DaveBerkeley/audio_selector/gateware/build.py

#!/usr/bin/env python

from amaranth import *
from amaranth.build import *

from audio_selector import System, get_resources

#
#

def ext_clock(freq, Platform, ck_name="ckext"):
    # Override the on-board clock with an external one
    class _Platform(Platform):
        default_clk = ck_name
        ck_freq = freq

    return _Platform()

#
#

if __name__ == "__main__":

    import argparse

    parser = argparse.ArgumentParser()
    parser.add_argument("--dot", help="generate Stream graph")
    parser.add_argument("--prog", action="store_true")
    parser.add_argument("--verbose", action="store_true")
    parser.add_argument("--freq", type=float, default=27e6*2)
    parser.add_argument("--platform", default="tangnano")
    parser.add_argument("--system")

    args = parser.parse_args()

    if args.platform == "tangnano":
        from tang_nano_dock import TangNanoDock as Platform
    elif args.platform == "i9":
        from colorlight_i9_r7_2 import Colorlight_i9_R72Platform as Platform
    elif args.platform == "icebreaker":
        from amaranth_boards.icebreaker import ICEBreakerPlatform as Platform
    elif args.platform == "icesugarnano":
        from amaranth_boards.icesugar_nano import ICESugarNanoPlatform as Platform

    freq = args.freq
    # external clock
    ext_freq = 48e3 * 512 # External MCK from I2S pin
    ext_freq = 48e3 * 1024 # External Xtal on PMOD
    freq = ext_freq

    platform = ext_clock(freq, Platform)

    r = get_resources(platform, args.platform, args.system, lang="Amaranth")
    platform.add_resources(r)

    # TODO : select other systems?
    dut = System(freq)
    # TODO : how are the clock constraints passed to Amaranth?
    #platform.add_clock_constraint(s, freq)

    platform.build(dut, do_program=args.prog, verbose=args.verbose)

    # Generate DOT graph of the Amaranth Streams
    if args.dot:
        from streams import dot
        dot_path = "/tmp/wifi.dot"
        png_path = args.dot
        dot.graph(dut, dot_path, png_path)

#   FIN
