DaveBerkeley/audio_selector/gateware/audio_selector.py

from amaranth import *
from amaranth.utils import bits_for

from streams import Stream, Join, Sink, Arbiter, Tee, Split
from streams.spi import SpiPeripheral
from streams.i2s import I2SRxClock, I2STxClock, I2SInputLR, I2SOutput
from streams.route import Router, Select
from streams.spdif import SPDIF_Tx, SPDIF_Rx
from streams.monitor import Monitor
from streams.ws2812 import LedStream
from streams.ops import Enumerate

#import pll

from gpio import GpioOut, GpioIn

from ppm import StereoAbs, PPM, BarGraph

audio = 16
audio_layout = [("data", audio)]
control = 32
control_layout = [("data", control)]
left_layout = [("left", audio)]
right_layout = [("right", audio)]
stereo_layout = left_layout + right_layout
led_layout = [("addr", 8), ("r", 8), ("g", 8), ("b", 8), ]

#
#

class TR:
    # Top-level Router 
    GPIO = 0
    LED = 1
    SELECT = 2
    MONITOR = 6
    KEYS = 16

routes = [
    #TR.GPIO,
    TR.LED,
    #TR.MONITOR,
    #TR.SELECT,
    TR.KEYS,
]

#
#

class UI(Elaboratable):

    KEY_SW = 0x01
    KEY_A  = 0x04
    KEY_B  = 0x02

    def __init__(self, chans=5):
        keys = 3
        leds = 8
        bright = 0xff
        self.nkeys = keys
        self.chans = chans
        self.bright = bright

        self.keys = Stream(layout=[("data", keys)], name="keys")
        self.i = Stream(layout=led_layout, name="i")
        self.o = Stream(layout=led_layout, name="o")

        self.key_state = Signal(keys)

        self.channel = Signal(range(chans))
        self.edit = Signal(range(chans))
        self.edit_mode = Signal()

        self.leds = leds
        self.led = Signal(range(leds+1))
        self.update = Signal()

    def elaborate(self, _):
        m = Module()

        with m.If(self.o.valid & self.o.ready):
            m.d.sync += self.o.valid.eq(0)
        with m.If(~self.i.ready):
            m.d.sync += self.i.ready.eq(1)
        with m.If(self.i.valid & self.i.ready):
            m.d.sync += self.i.ready.eq(0)
            # copy in to out, unless in edit_mode
            with m.If(~self.edit_mode):
                m.d.sync += self.o.valid.eq(1)
                m.d.sync += self.o.payload_eq(self.i.cat_payload(flags=True), flags=True)

        # Update LED output with the edit_mode state
        with m.If(self.update | self.led):
            with m.If(~self.o.valid):
                m.d.sync += [
                    self.o.valid.eq(1),
                    self.o.first.eq(self.led==0),
                    self.o.last.eq(self.led==(self.leds-1)),
                    self.o.addr.eq(self.led),
                    self.o.r.eq(0),
                    self.o.g.eq(0),
                    self.o.b.eq(0),

                    self.led.eq(self.led + 1),
                    self.update.eq(0),
                ]
                with m.If(self.led == self.channel):
                    m.d.sync += self.o.r.eq(self.bright)
                with m.If(self.led == self.edit):
                    m.d.sync += self.o.g.eq(self.bright)

                with m.If(self.led == (self.leds-1)):
                    m.d.sync += self.led.eq(0)

        with m.If((~self.keys.ready) & (self.led == 0)):
            m.d.sync += self.keys.ready.eq(1)

        key_on = Signal(self.nkeys)
        key_off = Signal(self.nkeys)
        key_diff = Signal(self.nkeys)
        m.d.comb += [
            key_on.eq(self.keys.data & ~self.key_state),
            key_off.eq(self.key_state & ~self.keys.data),
            key_diff.eq(self.key_state ^ self.keys.data),
        ]

        with m.If(self.keys.valid & self.keys.ready):
            m.d.sync += self.keys.ready.eq(0)
            m.d.sync += self.key_state.eq(self.keys.data)
            # process key input
            with m.If(self.edit_mode):
                # in edit mode
                with m.If(key_on & self.KEY_SW):
                    # enter the selection, exit edit_mode
                    m.d.sync += [
                        self.channel.eq(self.edit),
                        self.edit_mode.eq(0),
                    ]
                with m.If(key_on & self.KEY_A):
                    # change the channel
                    m.d.sync += [
                        self.update.eq(1),
                    ]
                    with m.If(self.keys.data & self.KEY_B):
                        # increment edit channel
                        with m.If(self.edit == (self.chans-1)):
                            m.d.sync += self.edit.eq(0)
                        with m.Else():
                            m.d.sync += self.edit.eq(self.edit + 1)
                    with m.Else():
                        # decrement edit channel
                        with m.If(self.edit == 0):
                            m.d.sync += self.edit.eq(self.chans - 1)
                        with m.Else():
                            m.d.sync += self.edit.eq(self.edit - 1)

            with m.Else():
                # currently in pass-thru mode
                with m.If(key_on & self.KEY_SW):
                    # switch to edit_mode
                    m.d.sync += [
                        self.edit_mode.eq(1),
                        self.edit.eq(self.channel),
                        self.update.eq(1),
                    ]

        return m

#
#

class Meter(Elaboratable):

    def __init__(self, thresholds=[]):
        self.mods = []
        self.connects = []

        led_width = 8
        bar_len = len(thresholds)
        bar_layout = [("data", led_width)]
        self.i = Stream(layout=stereo_layout, name="i")

        self.abs = StereoAbs(layout=stereo_layout)
        self.mods += [ self.abs ]
        self.connects += [ (self.i, self.abs.i) ]

        self.ppm = PPM(layout=audio_layout)
        self.mods += [ self.ppm ]
        self.connects += [ (self.abs.o, self.ppm.i) ]

        self.bars = BarGraph(iwidth=audio, owidth=led_width, thresholds=thresholds)
        self.mods += [ self.bars ]
        self.connects += [ (self.ppm.o, self.bars.i) ]

        self.enum = Enumerate(idx=[("addr", bits_for(bar_len-1))], layout=bar_layout, offset=0)
        self.mods += [ self.enum ]
        self.connects += [ (self.bars.o, self.enum.i) ]
 
        layout = self.enum.o.get_layout()
        self.o = Stream(layout=layout, name="o")
        self.connects += [ (self.enum.o, self.o) ]

    def elaborate(self, platform):
        m = Module()
        m.submodules += self.mods

        for a, b in self.connects:
            m.d.comb += Stream.connect(a, b)

        return m

#
#

class AudioSelector(Elaboratable):

    def __init__(self, freq):
        self.sys_ck = freq
        self.mods = []
        self.connects = []
        self.comb = []

        has_ci = True # add to TR items?

        if has_ci:
            self.in_arb = Arbiter(layout=control_layout, n=2)
            self.mods += [ self.in_arb ]

            self.ci = Stream(layout=control_layout, name="ci")
            self.connects += [ (self.ci, self.in_arb.i[0]) ]

        self.spi = SpiPeripheral(width=control, last_cs=True)
        self.mods += [ self.spi ]
        if has_ci:
            self.connects += [ (self.spi.o, self.in_arb.i[1]) ]

        sink = True
        self.router = Router(layout=control_layout, addr_field="data", addrs=routes, sink=sink)
        self.mods += [ self.router ]
        if has_ci:
            self.connects += [ (self.in_arb.o, self.router.i) ]
        else:
            self.connects += [ (self.spi.o, self.router.i) ]

        if TR.GPIO in routes:
            self.gpio_led = GpioOut(8, name="gpio.led")
            self.mods += [ self.gpio_led ]
            self.connects += [ (self.router.o[TR.GPIO], self.gpio_led.i) ]

        if TR.SELECT in routes:
            self.gpio_select = GpioOut(4, name="gpio.select")
            self.mods += [ self.gpio_select ]
            self.connects += [ (self.router.o[TR.SELECT], self.gpio_select.i) ]

        led_device = "ws2812" # "yf923"
        self.ws2812 = LedStream(N=8, sys_ck=freq, device=led_device)
        self.mods += [ self.ws2812 ]

        self.led_arb = Arbiter(layout=led_layout, n=2)
        self.mods += [ self.led_arb ]
        led_src = self.led_arb.o
 
        self.comb += self.ws2812.connect(self.router.o[TR.LED], self.led_arb.i[0])

        self.i2s_rxck = I2STxClock(width=32, owidth=16)
        self.mods += [ self.i2s_rxck ]

        self.i2s_txck = I2STxClock(width=16)
        self.mods += [ self.i2s_txck ]

        adcs = 4
        spdif_in = True
        selects = adcs
        if spdif_in:
            selects += 1

        self.l_select = Select(layout=[("data", audio)], n=selects, wait_last=False, sink=True)
        self.mods += [ self.l_select ]
        self.r_select = Select(layout=[("data", audio)], n=selects, wait_last=False, sink=True)
        self.mods += [ self.r_select ]

        self.i2si = []
        for i in range(adcs):
            label = f"i2s{i}"
            s = I2SInputLR(width=audio, rx_clock=self.i2s_rxck)
            self.mods += [ s ]
            setattr(self, label, s)
            self.i2si.append(s)

            self.connects += [ 
                (s.left, self.l_select.i[i]),
                (s.right, self.r_select.i[i]),
            ]

        self.join = Join(left=left_layout, right=right_layout)
        self.mods += [ self.join ]
        self.connects += [ (self.l_select.o, self.join.left, [], {"data":"left"}) ]
        self.connects += [ (self.r_select.o, self.join.right, [], {"data":"right"}) ]

        self.tee = Tee(layout=stereo_layout, n=3, wait_all=True)
        self.mods += [ self.tee ]
        self.connects += [ (self.join.o, self.tee.i), ]

        self.spdif = SPDIF_Tx(iwidth=audio)
        self.mods += [ self.spdif ]
        self.connects += [ (self.tee.o[0], self.spdif.i), ]
        self.spdif_o = Signal()

        self.i2so = I2SOutput(width=16, tx_clock=self.i2s_txck)
        self.mods += [ self.i2so ]
        self.connects += [ (self.tee.o[1], self.i2so.i), ]

        thresholds = [ 0x10, 0x80, 0x200, 0x800, 0x1000, 0x2000, 0x4000, 0x7fff  ]
        self.meter = Meter(thresholds=thresholds)
        self.mods += [ self.meter ]
        self.connects += [ (self.tee.o[2], self.meter.i) ]
        def dim(m, si, so):
            def _dim(name, src, dst):
                with m.If(si.addr >= 4):
                    m.d.sync += [
                        so.r.eq(src),
                        so.g.eq(0),
                    ]
                with m.Else():
                    m.d.sync += [
                        so.g.eq(src),
                        so.r.eq(0),
                    ]
                return []
            return _dim
        self.connects += [
            (self.meter.o, self.led_arb.i[1], ["g","b"], {"data":"g"}, {"data":dim}),
        ]

        if TR.KEYS in routes:
            self.gpio_ui = GpioIn(3, name="gpio.ui")
            self.mods += [ self.gpio_ui ]
            self.comb += [
                # Arbiter expects packets, so turn gpio data into a packet
                self.gpio_ui.o.first.eq(1),
                self.gpio_ui.o.last.eq(1),
            ]

            key_layout = self.gpio_ui.o.get_layout()
            self.key_arb = Arbiter(layout=key_layout, n=2) 
            self.mods += [ self.key_arb ]
            self.connects += [ (self.router.o[TR.KEYS], self.key_arb.i[0]) ]
            self.connects += [ (self.gpio_ui.o, self.key_arb.i[1]) ]

            self.ui = UI()
            self.mods += [ self.ui ]
            self.connects += [ (self.key_arb.o, self.ui.keys) ]
            self.connects += [ (self.led_arb.o, self.ui.i) ]
            led_src = self.ui.o

        self.connects += [ (led_src, self.ws2812.i) ]

        if spdif_in:
            self.rx = SPDIF_Rx(with_user=False, with_status=False)
            self.mods += [ self.rx ]
            layout_20 = [("left",20), ("right",20)]
            self.rx_split = Split(layout=layout_20)
            self.mods += [ self.rx_split ]

            def truncate(m, a, b):
                def to16(name, src, dst):
                    assert name in [ "left", "right" ], name
                    return [ dst.eq(src[4:]) ]
                return to16

            self.connects += [ 
                (self.rx.audio, self.rx_split.i, ["good"]),
                (self.rx_split.left, self.l_select.i[selects-1], [], {"left":"data"}, {"left":truncate}),
                (self.rx_split.right, self.r_select.i[selects-1], [], {"right":"data"}, {"right":truncate}),
            ]

            self.spdif_i = Signal()

        if TR.MONITOR in routes:
            self.monitor = Monitor(layout=audio_layout, n=8)
            self.mods += [ self.monitor ]
            self.connects += [ (self.router.o[TR.MONITOR], self.monitor.ci) ]

    def elaborate(self, platform):
        m = Module()
        m.submodules += self.mods

        for x in self.connects:
            a, b = x[:2]
            ex = x[2:3] or ([],)
            mm = x[3:4] or ({},)
            fn = x[4:5] or ({},)
            for k,v in fn[0].items():
                fn[0][k] = v(m, a, b)
            ex, mm, fn = ex[0], mm[0], fn[0]
            print(a, b, ex, mm, [ f"{k}:{v.__name__}" for k,v in fn.items() ])
            m.d.comb += Stream.connect(a, b, exclude=ex, mapping=mm, fn=fn)

        assert self.comb
        for eq in self.comb:
            print("comb", eq)
            m.d.comb += eq
        self.comb = []

        # The channel selection
        m.d.comb += [
            self.l_select.select.eq(self.ui.channel),
            self.r_select.select.eq(self.ui.channel),
        ]

        if hasattr(self, "monitor"):
            mons = [
                ("spi.o", self.spi.o, {}),
                #("gpio_ui.o", self.gpio_ui.o, {}),
                ("router.i", self.router.i, {}),
                #("gpio.led.i", self.gpio_led.i, {}),
                ("i2si[0].o", self.i2si[0].left, {}),
                ("l_select.i[0]", self.l_select.i[0], {}),
                #("l_select.i[1]", self.l_select.i[1], {}),
                #("l_select.i[2]", self.l_select.i[2], {}),
                #("l_select.i[3]", self.l_select.i[3], {}),
                ("l_select.o", self.l_select.o, {}),
                ("i2so.i", self.i2so.i, {"data":"left"}),
                #("join.o", self.join.o, {"data":"left"}),
                #("meter.o", self.meter.o, {}),
            ]

            for idx, (name, s, mm) in enumerate(mons):
                m.d.comb += self.monitor.tap(s, f"{idx}_" + name, idx, mm)

        # turning the rotational encoder can give a quadrature pulse ~ 4ms long
        debounce_freq = 1 / 4e-3
        clock_bits = bits_for(int(self.sys_ck / debounce_freq))
        counter = Signal(clock_bits)
        m.d.sync += counter.eq(counter + 1)
        # External Xtal is Fs * 1024
        self.fs_128 = Signal()
        self.fs_64  = Signal()
        m.d.comb += self.fs_128.eq((counter & 0x07) == 0)
        m.d.comb += self.fs_64.eq ((counter & 0x0f) == 0)

        # Fs * 512 for the MCK I2S input master ref
        self.mck = Signal()
        m.d.comb += self.mck.eq(counter) # square wave : sys_ck/2
        # Fs * 128 for the SPDIF 2*clock signal
        m.d.comb += self.spdif.en.eq(self.fs_128)
        # Fs * 128 for the I2S input 2*clock signal
        m.d.comb += self.i2s_rxck.enable.eq(self.fs_128)
        # Fs * 64 for the I2S output 2*clock signal
        m.d.comb += self.i2s_txck.enable.eq(self.fs_64)

        # debounce (sample) clock for the UI buttons
        self.debounce = Signal()
        m.d.sync += self.debounce.eq(counter == 0)
        m.d.sync += self.gpio_ui.en.eq(self.debounce)

        # connect the SPDIF io to spdif_i/o
        if hasattr(self, "rx"):
            idx = len(self.l_select.i) - 1
            with m.If(self.ui.channel == idx):
                # loop spdif input to the output
                m.d.comb += [ self.spdif_o.eq(self.spdif_i) ]
            with m.Else():
                m.d.comb += [ self.spdif_o.eq(self.spdif.o) ]
            m.d.comb += self.rx.i.eq(self.spdif_i) 
        else:
            m.d.comb += self.spdif_o.eq(self.spdif.o)
        return m

#
#

class _System(AudioSelector):

    # Connect all the application specific io
    def __init__(self, *args, **kwargs):
        super().__init__(*args, **kwargs)
        #limits = pll.get_limits(25, 55, device)
        #self.pll = pll.PLL(27, 55, limits)
        #self.counter_s = Signal(20)
        #self.counter_a = Signal(20)

    def do_connect(self, platform):
        comb = []

        if platform is None:
            # LiteX doesn't pass in a platform,
            # so use the Amaranth one for all the application
            # specific connections.
            platform = self.platform
            wrapper = platform.wrapper
            def from_i(s): return wrapper.from_migen(s)
            def to_o(s): return wrapper.from_migen(s)
        else:
            def from_i(s): return s.i
            def to_o(s): return s.o

        spi = platform.request("spi", 0)

        comb += [
            self.spi.phy.scs.eq(from_i(spi.cs)),
            self.spi.phy.sck.eq(from_i(spi.sck)),
            self.spi.phy.copi.eq(from_i(spi.copi)),
        ]

        spdif = platform.request("spdif", 0)
        comb += [ 
            self.spdif_i.eq(from_i(spdif.rx)),
            to_o(spdif.tx).eq(self.spdif_o),
        ]

        # I2S output monitor
        try:
            i2s = platform.request("i2s", 1)
            comb += [
                to_o(i2s.sck).eq(self.i2so.phy.sck),
                to_o(i2s.ws).eq(self.i2so.phy.ws),
                to_o(i2s.sd).eq(self.i2so.phy.sd),
            ]
        except Exception as ex:
            print(ex)

        # I2S output wifi server
        try:
            i2s = platform.request("i2s", 2)
            comb += [
                to_o(i2s.sck).eq(self.i2so.phy.sck),
                to_o(i2s.ws).eq(self.i2so.phy.ws),
                to_o(i2s.sd).eq(self.i2so.phy.sd),
            ]
        except Exception as ex:
            print(ex)

        # I2S input block from ADCs
        try:
            i2s = platform.request("i2s", 0)
            # connect the I2S timing to the rx_clock
            comb += [
                to_o(i2s.sck).eq(self.i2s_rxck.sck),
                to_o(i2s.ws).eq(self.i2s_rxck.ws),
                to_o(i2s.mck).eq(self.mck),
            ]
            # connect the I2S data inputs
            for i, i2si in enumerate(self.i2si):
                s = getattr(i2s, f"d{i}")
                comb += [ i2si.i.eq(from_i(s)) ]
        except Exception as ex:
            print(ex)
            raise

        try:
            ws2812 = platform.request("ws2812", 0)
            comb += [ to_o(ws2812).eq(self.ws2812.o) ]
        except Exception as ex:
            print(ex)

        # connect the rotary switch
        try:
            sw = platform.request("sw", 0)
            # invert the signals, so the switch gives 1 on press
            comb += [ self.gpio_ui.i.eq(~from_i(sw)) ]
        except Exception as ex:
            print(ex)

        if hasattr(self, "monitor"):
            s = self.monitor.o0
            sd = self.monitor.o0.data
        else:
            s = self.join.o
            sd = s.left

        try:
            test = platform.request("test", 0)
            dev = self.i2si[0]

            comb += [
                to_o(test).eq(Cat(
                    s.valid,
                    s.ready,
                    #s.first,
                    #s.last,
                    #sd,
                    #i2s.mck.o, 
                    i2s.sck.o, i2s.ws.o, i2s.d0.i, i2s.d1.i, i2s.d2.i, i2s.d3.i,
                    #dev.rx_clock.sck, dev.rx_clock.ws,
                    #dev.rx_clock.l_word, dev.rx_clock.r_word,

                )),
            ]
        except Exception as ex:
            print(ex)
            raise

        try:
            test = platform.request("test", 1)

            comb += [
                to_o(test).eq(Cat(
                    sd,
                )),
            ]
        except Exception as ex:
            print(ex)

        self.comb += comb
        return comb

    def elaborate(self, platform):
        m = super().elaborate(platform)

        if self.comb:
            m.d.comb += self.comb
        else:
            m.d.comb += self.do_connect(platform)

        #m.submodules += self.pll

        #m.d.comb += [
        #    self.pll.clk_in.eq(platform.request("clk27").i),
        #    self.pll.rst_in.eq(0),
        #]

        #m.domains.audio = ClockDomain("audio")
        #m.d.sync += self.counter_s.eq(self.counter_s+1)
        #m.d.audio += self.counter_a.eq(self.counter_a+1)

        return m

#
#

class System(_System):

    # Connect any board/platform specific io

    def elaborate(self, platform):
        m = super().elaborate(platform)

        # Connect the on-board LEDs to the GPIO
        i = 0
        leds = []
        while True:
            try:
                led = platform.request("led", i)
                leds.append(led.o)
                i += 1
            except Exception as ex:
                print(ex)
                break
        leds = Cat(leds)

        if hasattr(self, "gpio_led"):
            m.d.comb += leds.eq(Cat(self.gpio_led.o))
        else:
            m.d.comb += leds.eq(1 << self.l_select.select)

        return m

#
#

def get_resources(platform, platform_name, system, lang="Amaranth"):
    from io_defs import set_platform
    from io_defs import make_i2s_o, make_spdif, make_spi, make_test
    from io_defs import make_clock, make_i2s_backplane, make_io

    print("build for", platform_name)

    set_platform(platform, lang=lang)

    try:
        family = platform.family
    except AttributeError:
        family = platform.devicename

    def make_io_board(conn):
        # audio selector PCB. see LinuxNotes_07-Dec-2025
        r = []
        r += make_spi(conn=conn, order="4 3 2 1") # cs, sck, copi, cipo
        r += make_spdif(conn=conn, idx=0, order="10 9") # rx tx
        r += make_io("ws2812", idx=0, _pins="7", _dir="o", conn=conn, v="3V3")
        r += make_clock(freq=49.152e6, _pin="8", name="ckext", conn=conn)
        return r

    if platform_name == "tangnano":
        # TangNano 9k
        pmod_io    = ("pmod", 0)
        pmod_i2si  = ("pmod", 1)
        pmod_i2so  = ("pmod", 4)
        pmod_aux   = ("pmod", 5)
        pmod_test  = ("pmod", 2)
        #pmod_test2  = ("pmod", 4)
        pmod_sw    = ("pmod", 3) # 1V8 port

        r = []
        r += make_test(conn=pmod_test) # , order="1 2 3 4 8 9 10") # skip the 1V8 pin for now!
        #r += make_test(conn=pmod_test2, idx=1, order="1 2 3 4 8 9 10") # skip the 1V8 pin for now!
        r += make_i2s_backplane(conn=pmod_i2si, idx=0, controller=True)
        r += make_i2s_o(conn=pmod_i2so, idx=1)
        r += make_io("sw", idx=0, _pins="4 3 2", _dir="i", conn=pmod_sw, v="1V8", pull="up")
        r += make_io_board(pmod_io)
        # aux connection for wifi RTPS server
        r += make_i2s_o(conn=pmod_aux, idx=2, order="7 8 9")

        return r

    if platform_name == "i9":
        # TODO : experimental
        # colorlight i9
        # TODO
        pmod_i2so  = ("pmod", 4)
        pmod_sw    = ("pmod", 5)
        pmod_io    = ("pmod", 6)
        pmod_i2si  = ("pmod", 7)
        pmod_test  = ("pmod", 8)
        pmod_test2 = ("pmod", 9)

        r = []
        r += make_test(idx=0, conn=pmod_test)
        r += make_test(idx=1, conn=pmod_test2)
        r += make_i2s_backplane(conn=pmod_i2si, idx=0, controller=True)
        r += make_i2s_o(conn=pmod_i2so, idx=1)
        r += make_io("sw", idx=0, _pins="4 3 2", _dir="i", conn=pmod_sw, v="3V3", pull="up")
        r += make_io_board(pmod_io)
        return r

    if platform_name == "icebreaker":
        # TODO
        assert system == "hatchat", system
        pmod_i2si  = ("pmod", 0)
        pmod_io    = ("pmod", 1)
        pmod_sw    = ("pmod", 2)
        pmod_i2so  = ("pmod", 2)

        r = []
        r += make_i2s_backplane(conn=pmod_i2si, idx=0)
        r += make_i2s_o(conn=pmod_i2so, idx=1)
        r += make_io("sw", idx=0, _pins="10 9 8", _dir="i", conn=pmod_sw, v="3V3", pull="up")
        r += make_io_board(pmod_io)
        return r

    if platform_name == "icesugarnano":
        # TODO
        assert system == "hatchat", system
        pmod_i2si  = ("pmod", 0)
        pmod_io    = ("pmod", 1)
        pmod_sw    = ("pmod", 2)
        pmod_i2so  = ("pmod", 2)

        r = []
        #r += make_i2s_backplane(conn=pmod_i2si, idx=0)
        #r += make_i2s_o(conn=pmod_i2so, idx=1)
        r += make_io("sw", idx=0, _pins="10 9 8", _dir="i", conn=pmod_sw, v="3V3", pull="up")
        #r += make_io_board(pmod_io)
        return r

    assert 0, (family, platform, platform_name)

#   FIN
